RaduTul/Proiect-TSC/Images/baterie.PNG

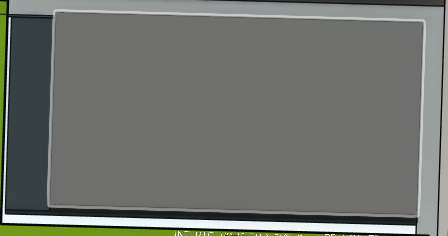
Images/baterie.PNG
