RaduTul/Proiect-TSC/Images/inclinat3ddupareview.PNG

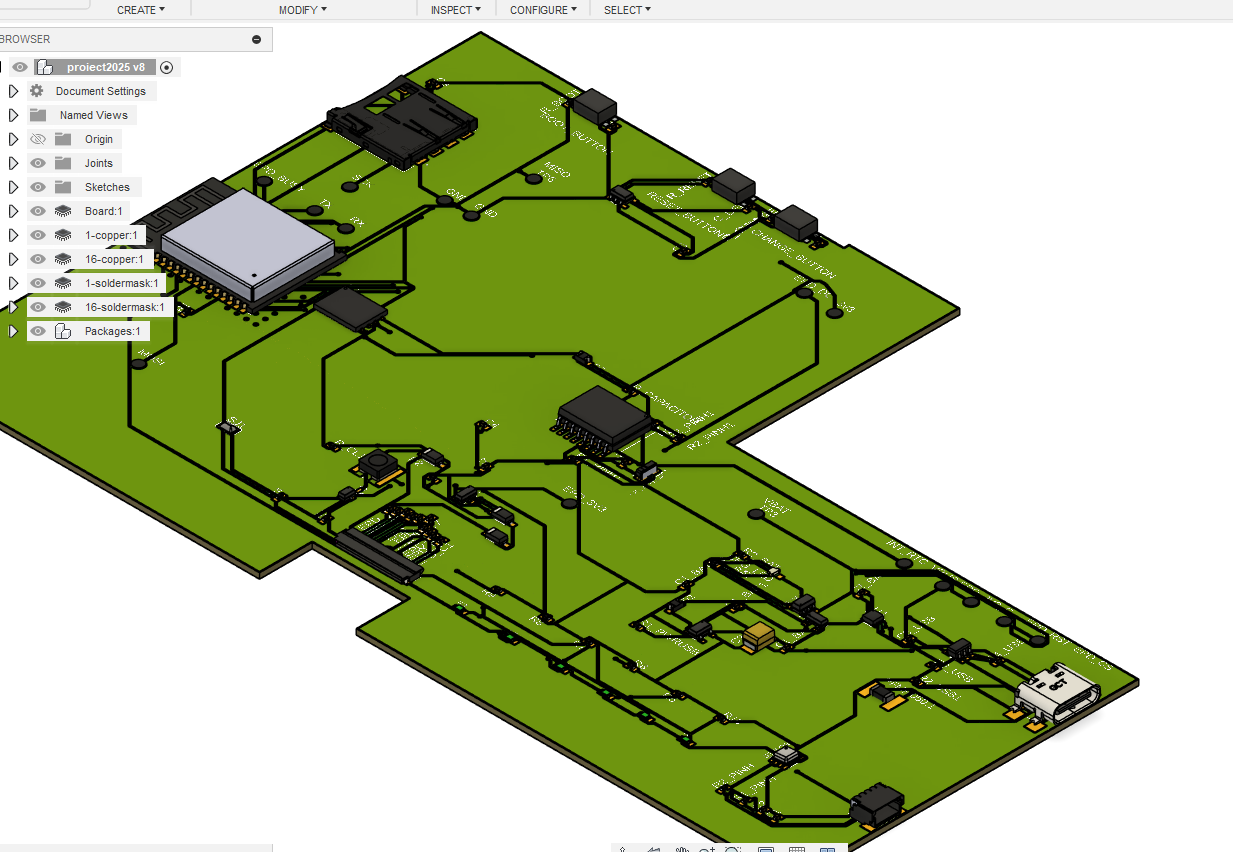
Images/inclinat3ddupareview.PNG
